kyuucr/Neptunewire/STLS/Gantry/XZ_Axis/X_Carriage/probe_retainer_bracket.stl

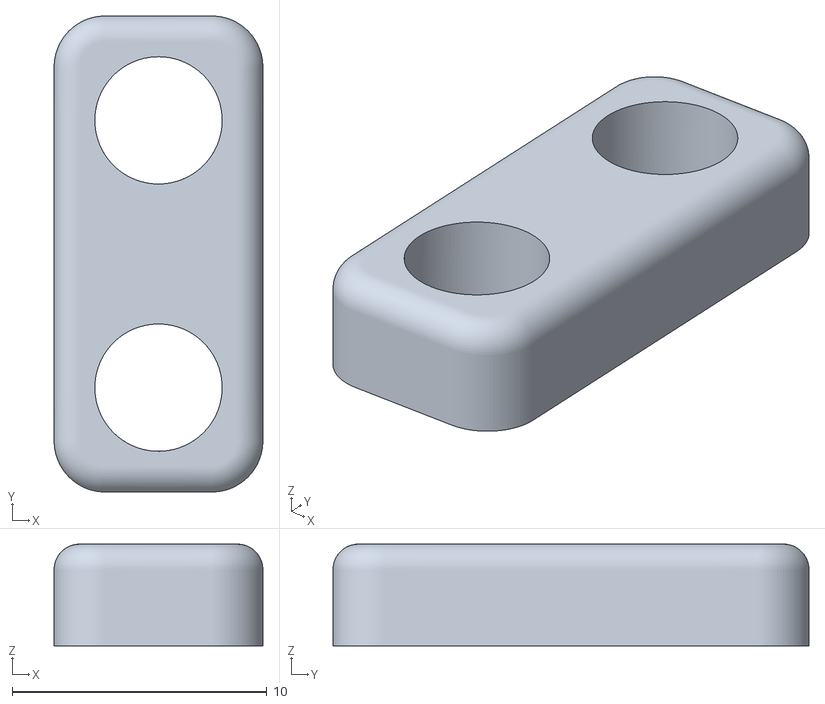
[picture p15: CAD file, 2026-07-10]
STLS/Gantry/XZ_Axis/X_Carriage/probe_retainer_bracket.stl
8.20 x 18.7 x 4.00
