kyuucr/Neptunewire/STLS/Gantry/Y_Axis/[a]_y_chain_frame_mount_igus.stl

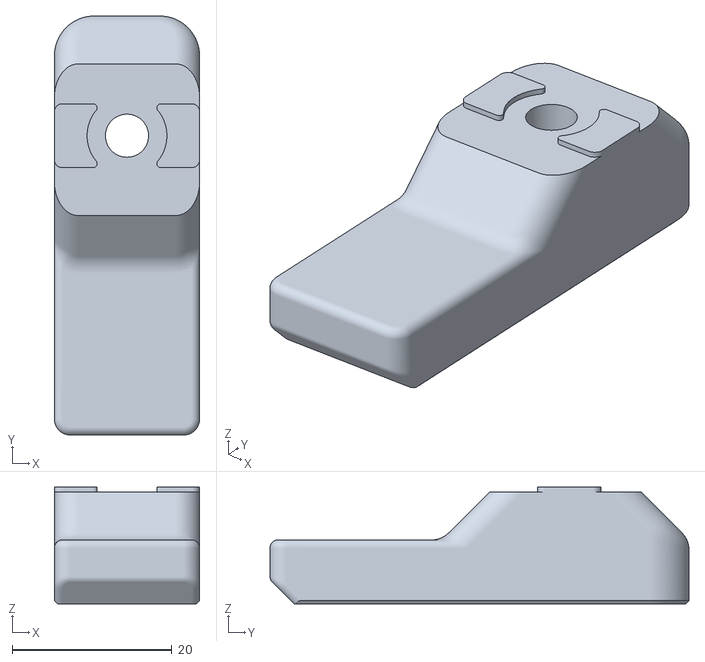
[picture p16: CAD file, 2026-07-10]
STLS/Gantry/Y_Axis/[a]_y_chain_frame_mount_igus.stl
18.2 x 52.5 x 14.6
