kyuucr/Neptunewire/STLS/Grills/grill_rear_left.stl

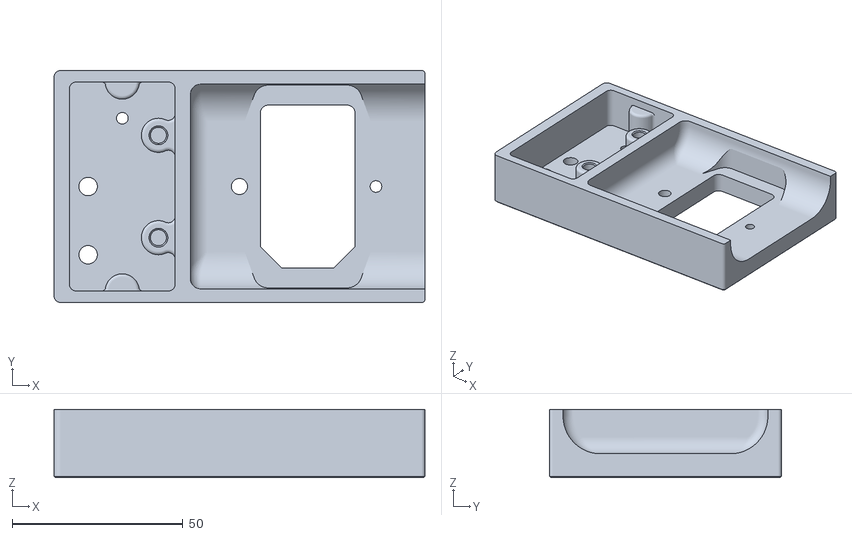
[picture p17: CAD file, 2026-07-10]
STLS/Grills/grill_rear_left.stl
108.7 x 68.0 x 20.0
