kyuucr/Neptunewire/STLS/Panel_Mounting/Doors/top_door_latch.stl

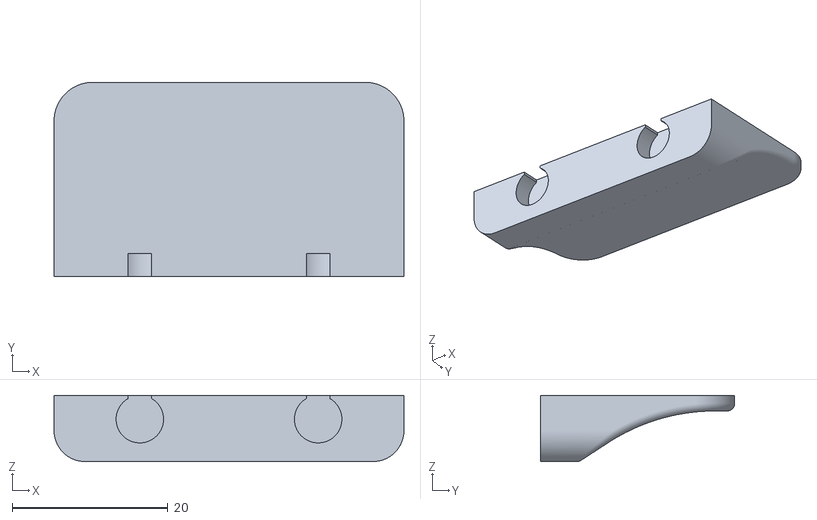
[picture p18: CAD file, 2026-07-10]
STLS/Panel_Mounting/Doors/top_door_latch.stl
45.0 x 25.0 x 8.50
