kyuucr/Neptunewire/STLS/Panel_Mounting/side_strap_x4.stl

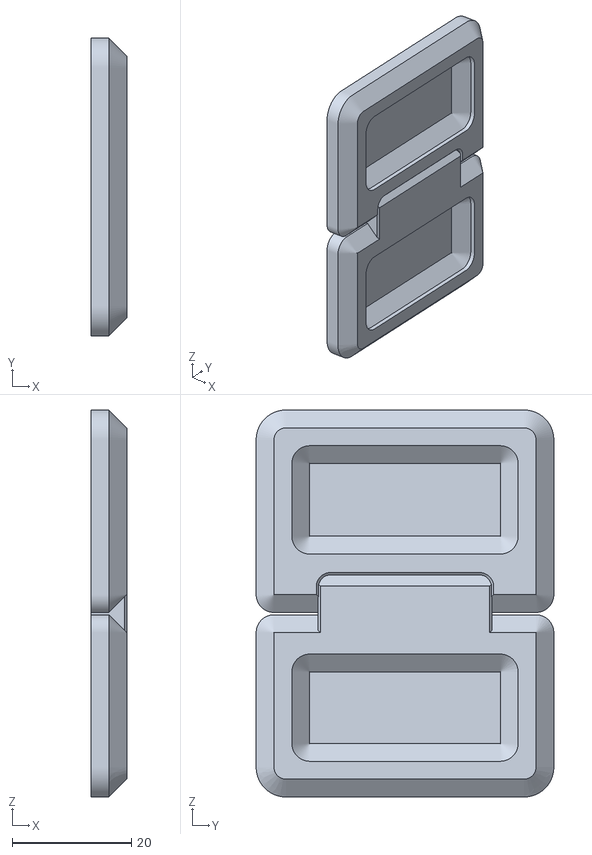
[picture p19: CAD file, 2026-07-10]
STLS/Panel_Mounting/side_strap_x4.stl
6.00 x 50.0 x 65.0
