kyuucr/Neptunewire/STLS/Decks_Printable/deck_right_front.stl

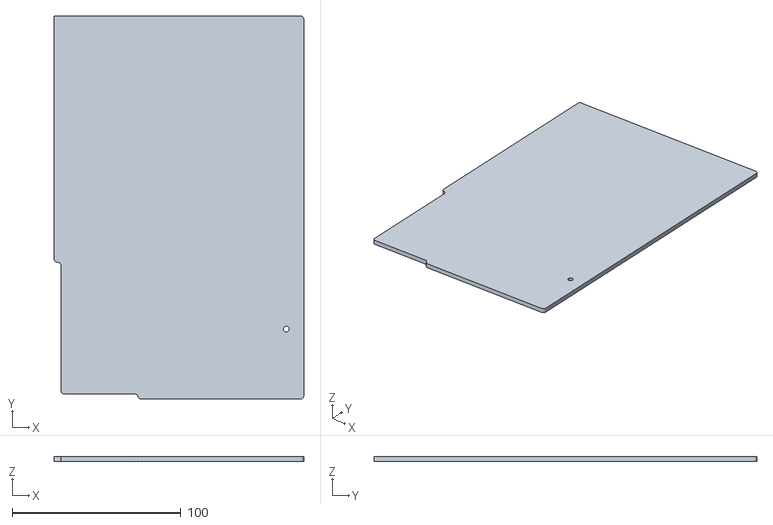
[picture p20: CAD file, 2026-07-10]
STLS/Decks_Printable/deck_right_front.stl
148.0 x 227.0 x 3.00
