kyuucr/Neptunewire/STLS/Electronics/PS_board_4040_mount.stl

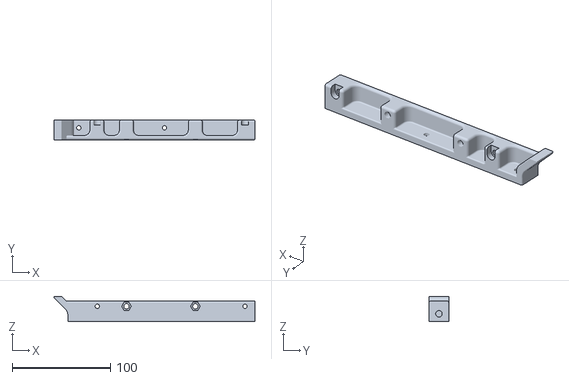
[picture p21: CAD file, 2026-07-10]
STLS/Electronics/PS_board_4040_mount.stl
204.2 x 20.1 x 25.8
