kyuucr/Neptunewire/STLS/Extensions/rear_extension_right_a.stl

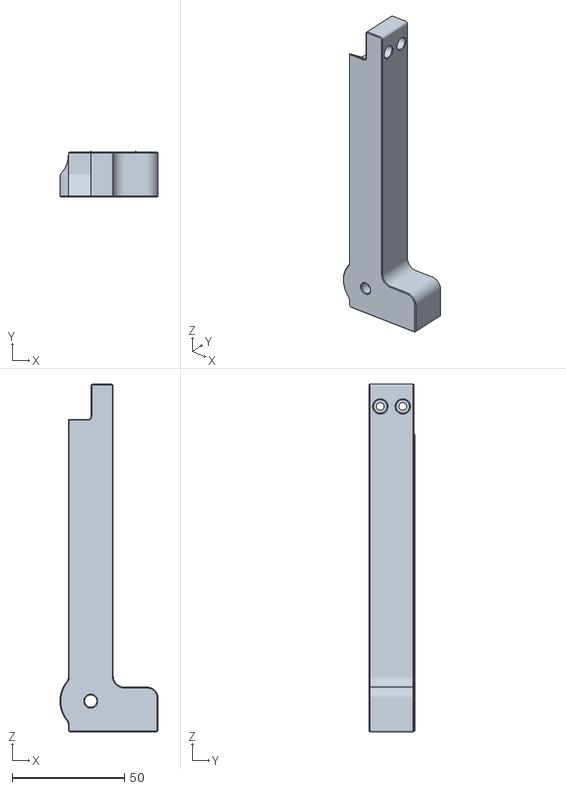
[picture p22: CAD file, 2026-07-10]
STLS/Extensions/rear_extension_right_a.stl
43.8 x 20.4 x 154.9
