kyuucr/Neptunewire/STLS/Gantry/XZ_Axis/X_Carriage/[a]_x_bearing_block.stl

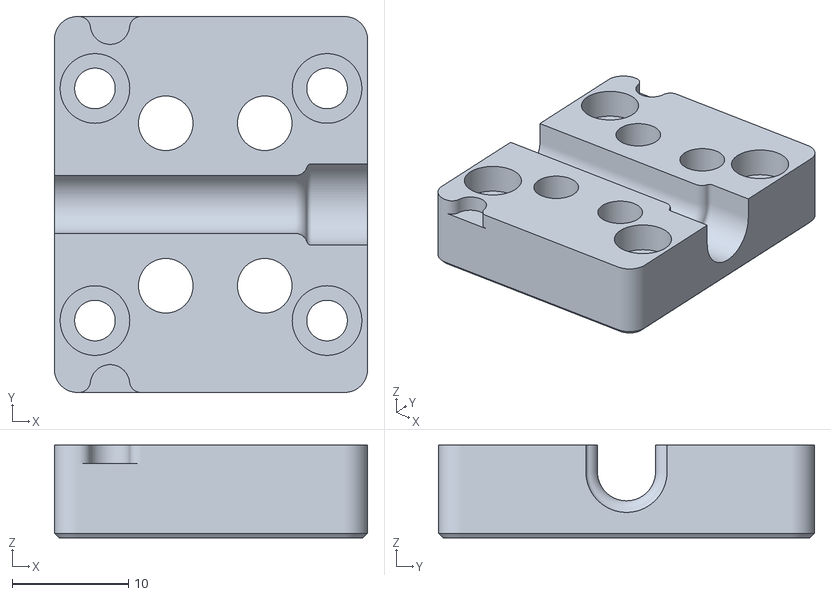
[picture p23: CAD file, 2026-07-10]
STLS/Gantry/XZ_Axis/X_Carriage/[a]_x_bearing_block.stl
27.0 x 32.4 x 8.00
