kyuucr/Neptunewire/STLS/Gantry/XZ_Axis/x_motor_mount_b.stl

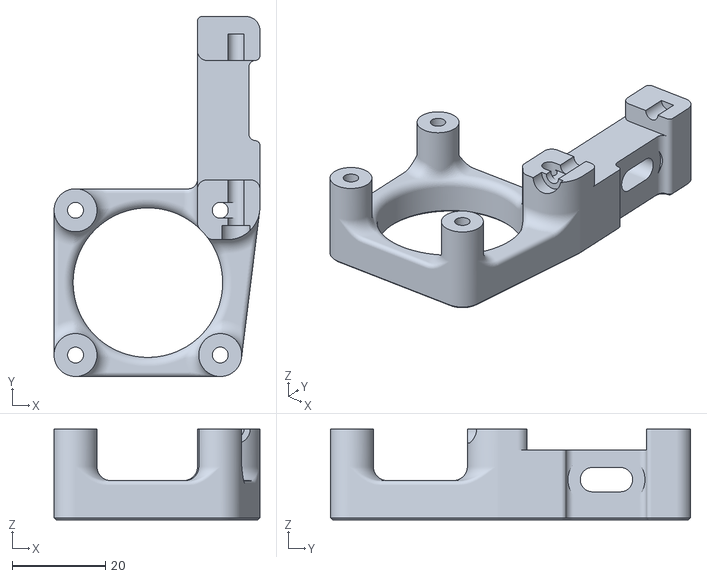
[picture p24: CAD file, 2026-07-10]
STLS/Gantry/XZ_Axis/x_motor_mount_b.stl
44.1 x 77.1 x 19.4
