kyuucr/Neptunewire/STLS/Gantry/Y_Axis/[a]_y_chain_bed_mount_generic.stl

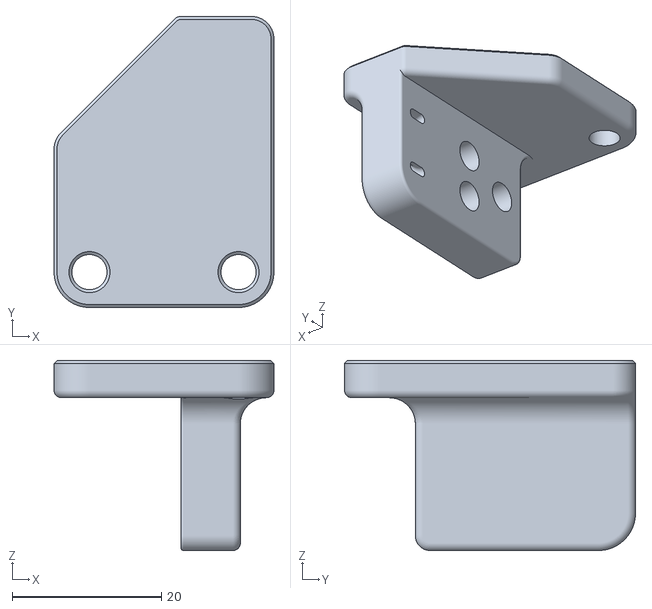
[picture p25: CAD file, 2026-07-10]
STLS/Gantry/Y_Axis/[a]_y_chain_bed_mount_generic.stl
29.5 x 39.0 x 25.5
