kyuucr/Neptunewire/STLS/Grills/grill_front_middle.stl

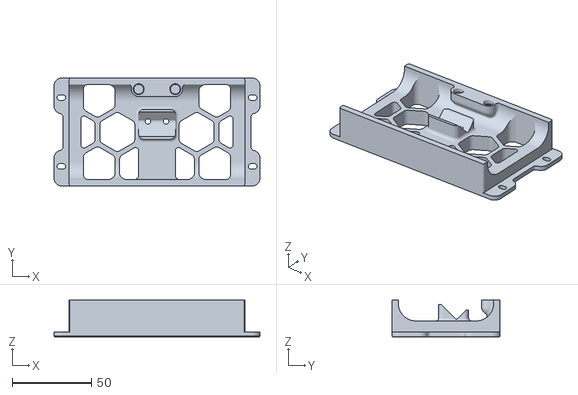
[picture p26: CAD file, 2026-07-10]
STLS/Grills/grill_front_middle.stl
129.8 x 68.0 x 23.0
