kyuucr/Neptunewire/STLS/Panel_Mounting/Doors/door_handle_a_x2.stl

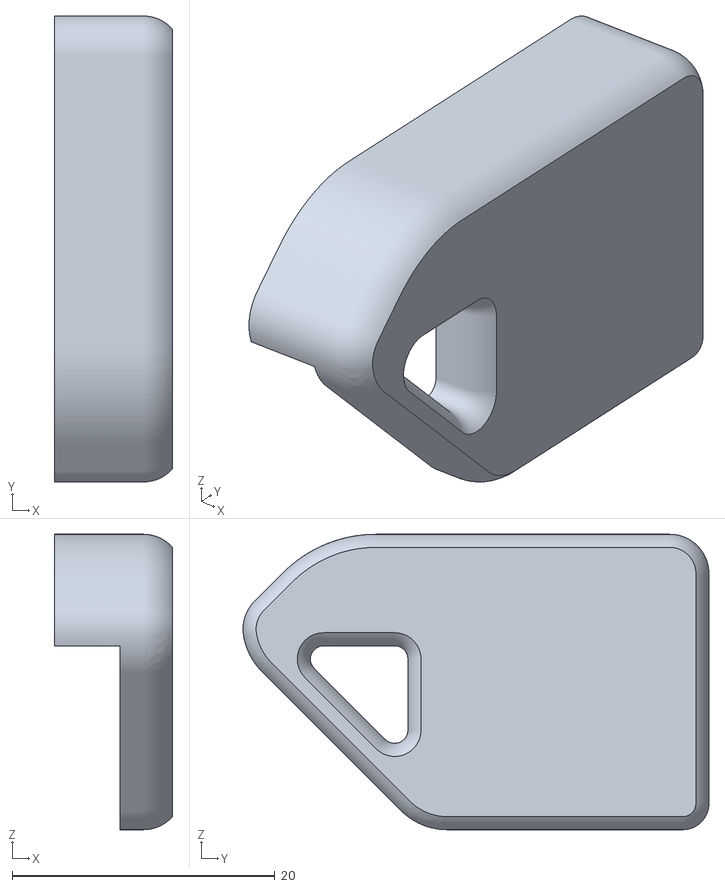
[picture p27: CAD file, 2026-07-10]
STLS/Panel_Mounting/Doors/door_handle_a_x2.stl
9.00 x 35.5 x 22.5
