kyuucr/Neptunewire/STLS/Panel_Mounting/panel_clip_x4.stl

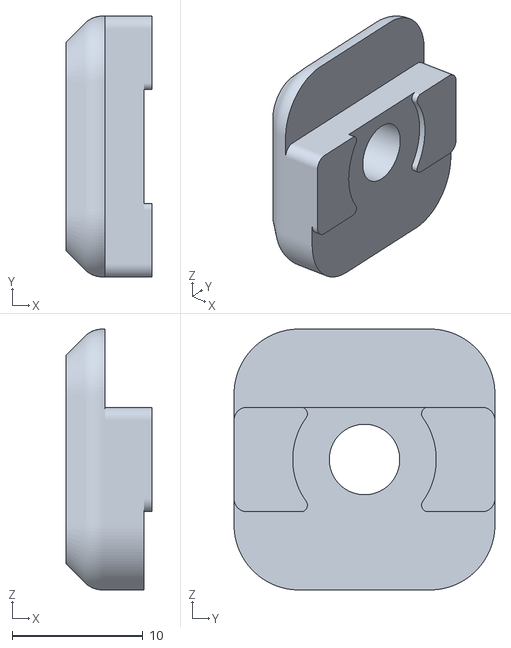
[picture p28: CAD file, 2026-07-10]
STLS/Panel_Mounting/panel_clip_x4.stl
6.60 x 20.0 x 20.0
