kyuucr/Neptunewire/STLS/Electronics/hex_board_frame_skr_pico+fly_utor.stl

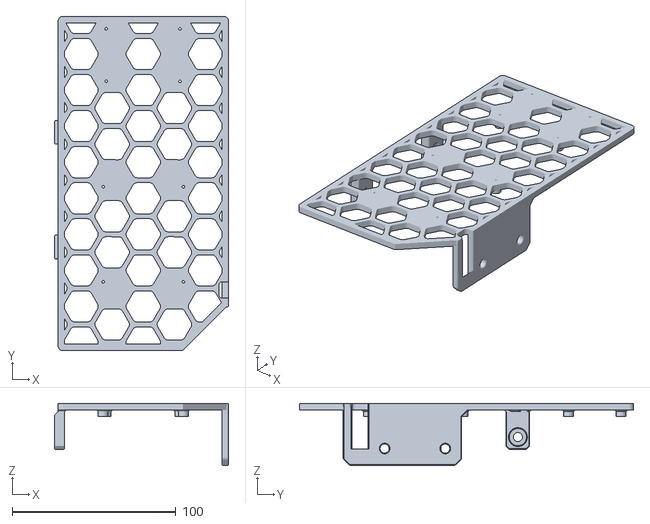
[picture p29: CAD file, 2026-07-10]
STLS/Electronics/hex_board_frame_skr_pico+fly_utor.stl
106.2 x 204.0 x 37.9
