kyuucr/Neptunewire/STLS/Gantry/XZ_Axis/X_Carriage/[a]_xz_belt_clip_x2.stl

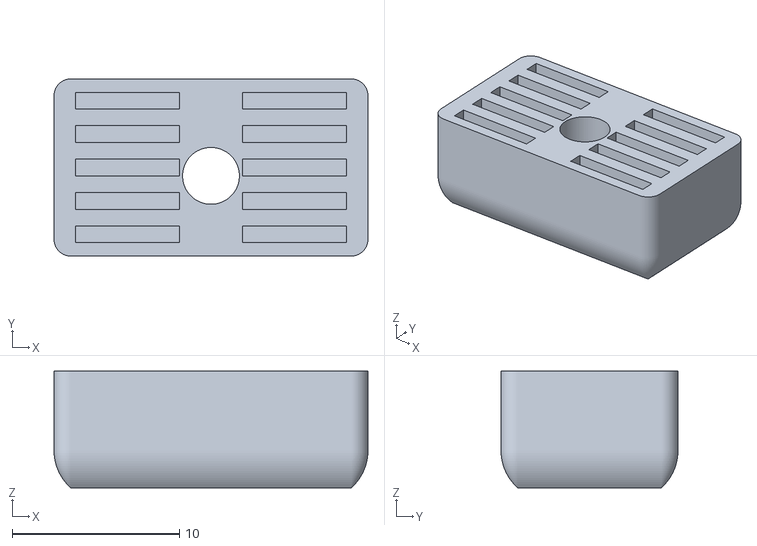
[picture p30: CAD file, 2026-07-10]
STLS/Gantry/XZ_Axis/X_Carriage/[a]_xz_belt_clip_x2.stl
18.8 x 10.6 x 7.00
