kyuucr/Neptunewire/STLS/Gantry/Y_Axis/[a]_y_axis_ls_mount.stl

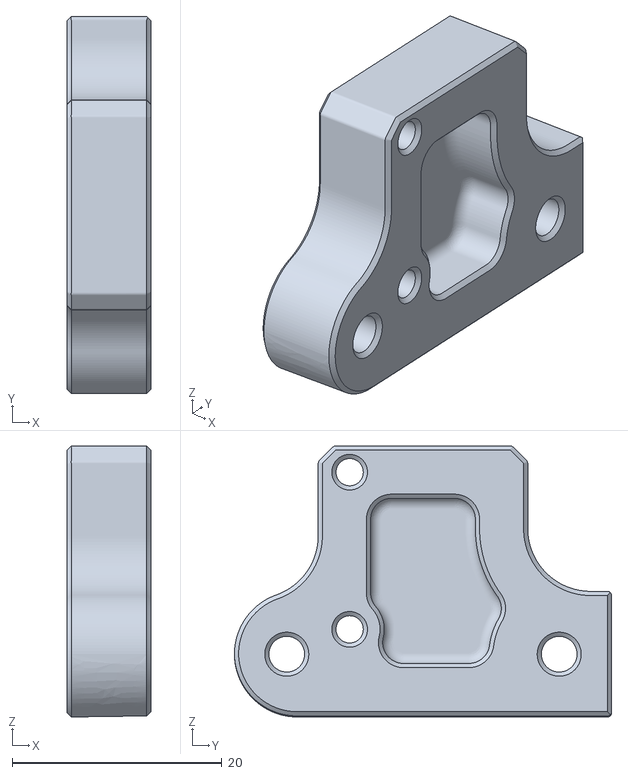
[picture p31: CAD file, 2026-07-10]
STLS/Gantry/Y_Axis/[a]_y_axis_ls_mount.stl
8.00 x 36.0 x 25.9
