kyuucr/Neptunewire/STLS/Grills/grill_rear_middle.stl

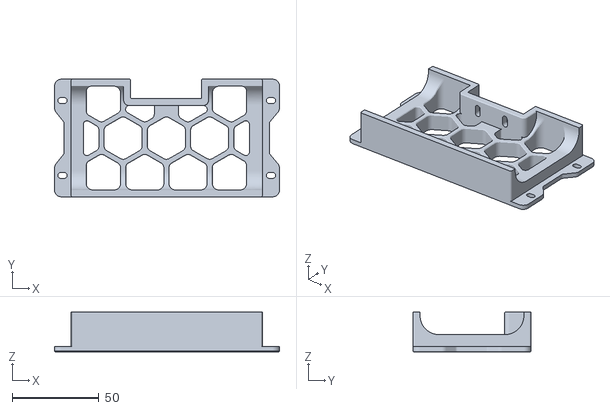
[picture p32: CAD file, 2026-07-10]
STLS/Grills/grill_rear_middle.stl
130.0 x 68.0 x 23.0
