kyuucr/Neptunewire/STLS/Panel_Mounting/front_panel_bracket_left.stl

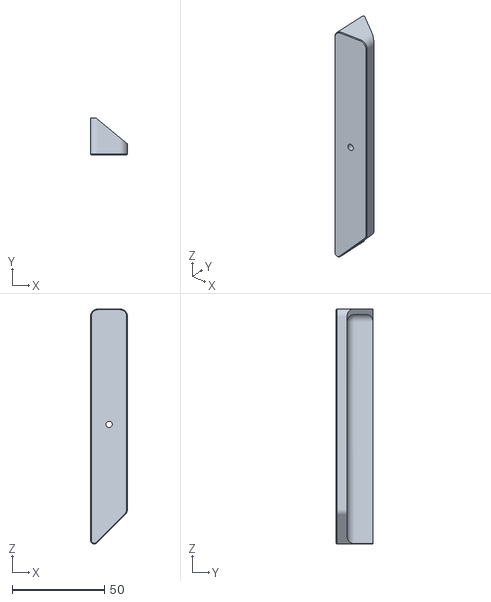
[picture p33: CAD file, 2026-07-10]
STLS/Panel_Mounting/front_panel_bracket_left.stl
20.0 x 20.0 x 127.2
