kyuucr/Neptunewire/STLS/Electronics/hex_board_frame.stl

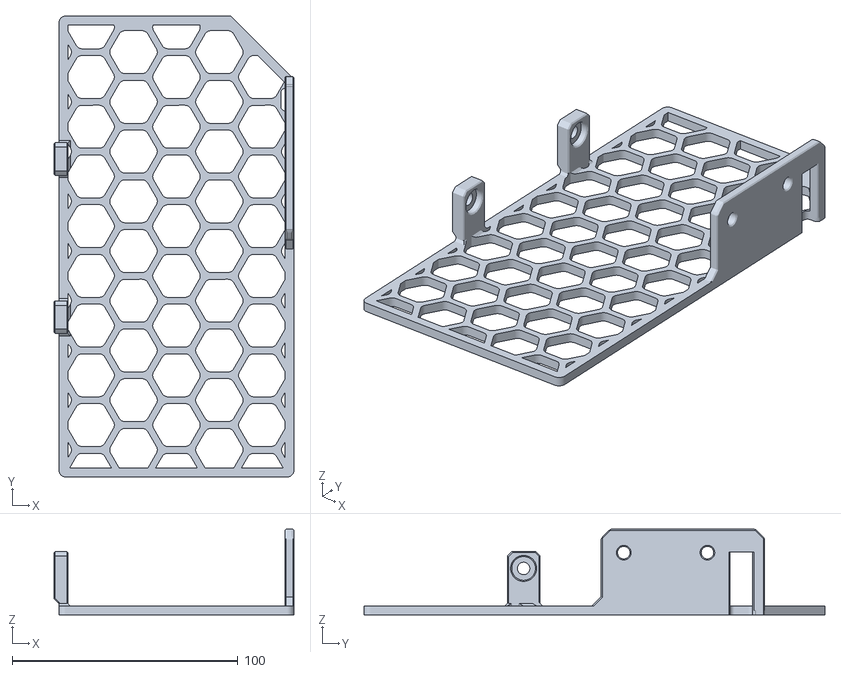
[picture p34: CAD file, 2026-07-10]
STLS/Electronics/hex_board_frame.stl
106.2 x 204.0 x 37.9
