kyuucr/Neptunewire/STLS/Extensions/front_extension_left_b.stl

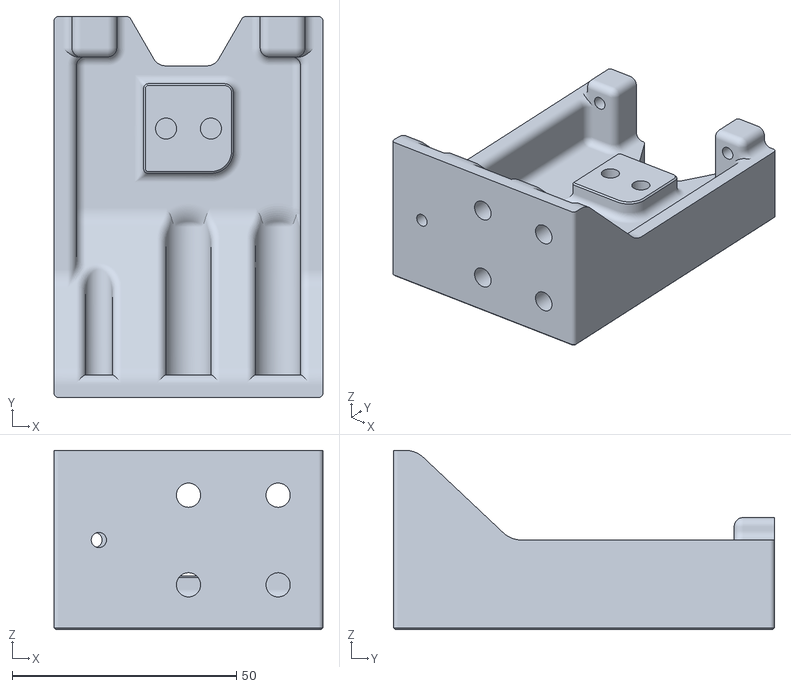
[picture p35: CAD file, 2026-07-10]
STLS/Extensions/front_extension_left_b.stl
60.0 x 85.0 x 40.0
