kyuucr/Neptunewire/STLS/Gantry/XZ_Axis/xz_block_right_b.stl

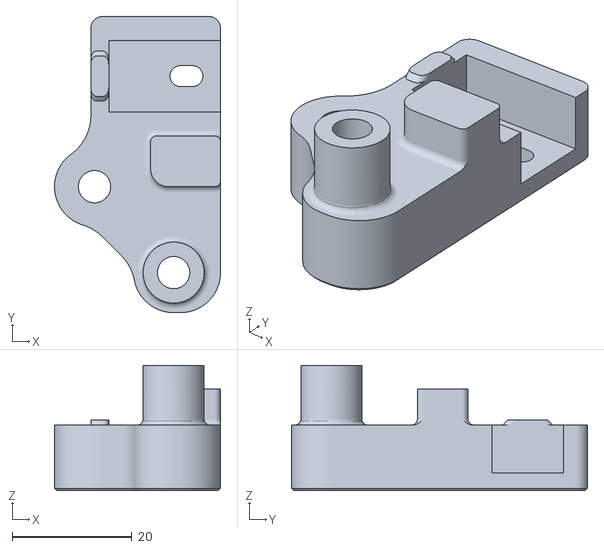
[picture p36: CAD file, 2026-07-10]
STLS/Gantry/XZ_Axis/xz_block_right_b.stl
27.8 x 49.6 x 21.0
