kyuucr/Neptunewire/STLS/Grills/grill_rear_left_shock_blocker.stl

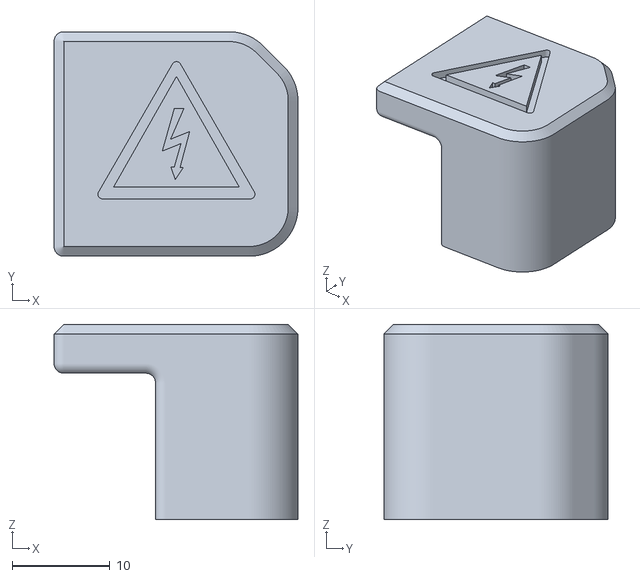
[picture p37: CAD file, 2026-07-10]
STLS/Grills/grill_rear_left_shock_blocker.stl
25.0 x 23.0 x 20.0
