kyuucr/Neptunewire/STLS/Decks_Printable/deck_right_rear.stl

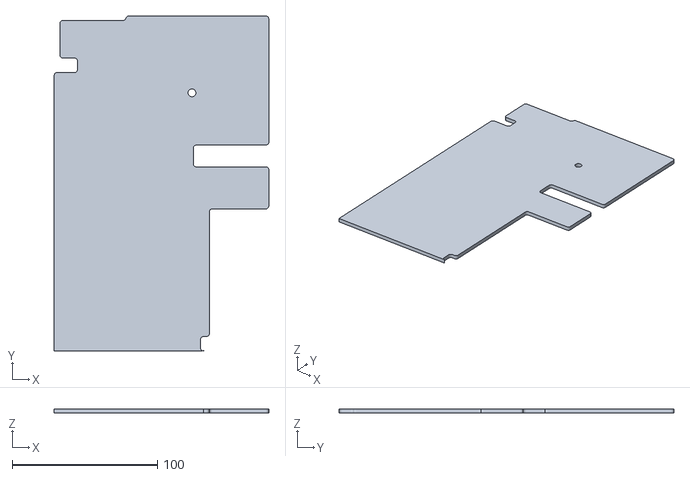
[picture p38: CAD file, 2026-07-10]
STLS/Decks_Printable/deck_right_rear.stl
148.0 x 231.0 x 3.00
