kyuucr/Neptunewire/STLS/Extensions/rear_extension_left_b.stl

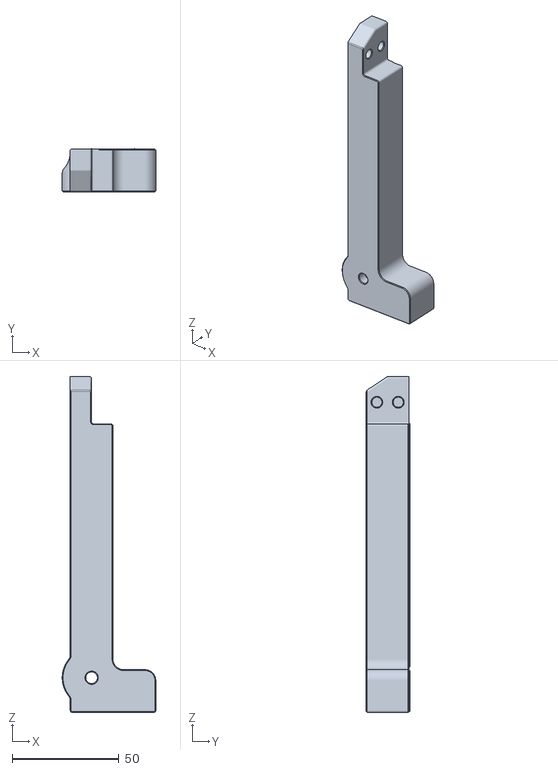
[picture p39: CAD file, 2026-07-10]
STLS/Extensions/rear_extension_left_b.stl
43.7 x 20.4 x 157.1
