kyuucr/Neptunewire/STLS/Gantry/XZ_Axis/keybak_mount_plate_b.stl

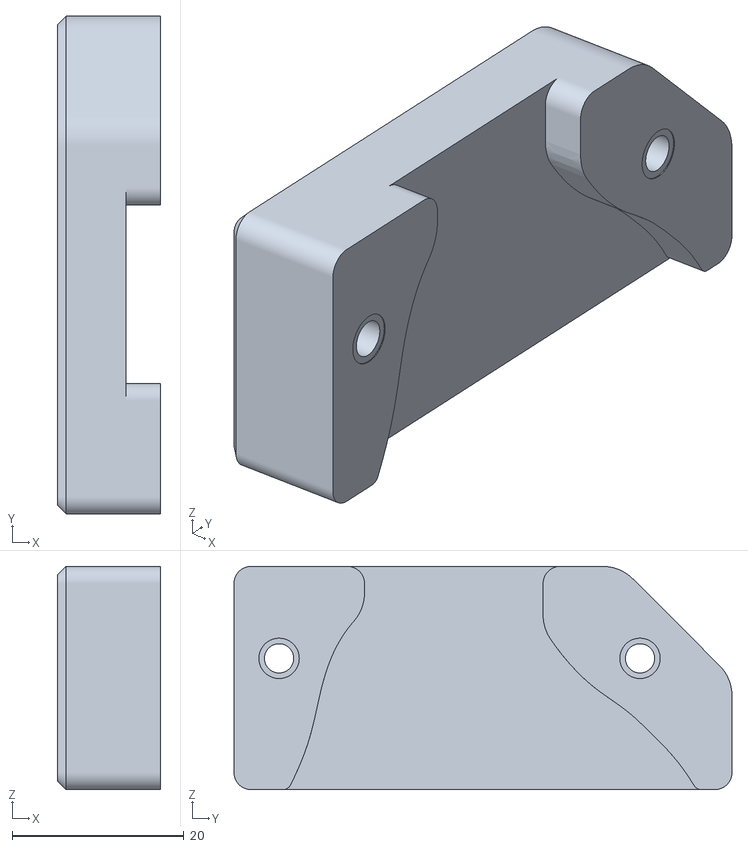
[picture p40: CAD file, 2026-07-10]
STLS/Gantry/XZ_Axis/keybak_mount_plate_b.stl
12.0 x 58.0 x 26.0
