kyuucr/Neptunewire/STLS/Gantry/Y_Axis/y_idler_inner.stl

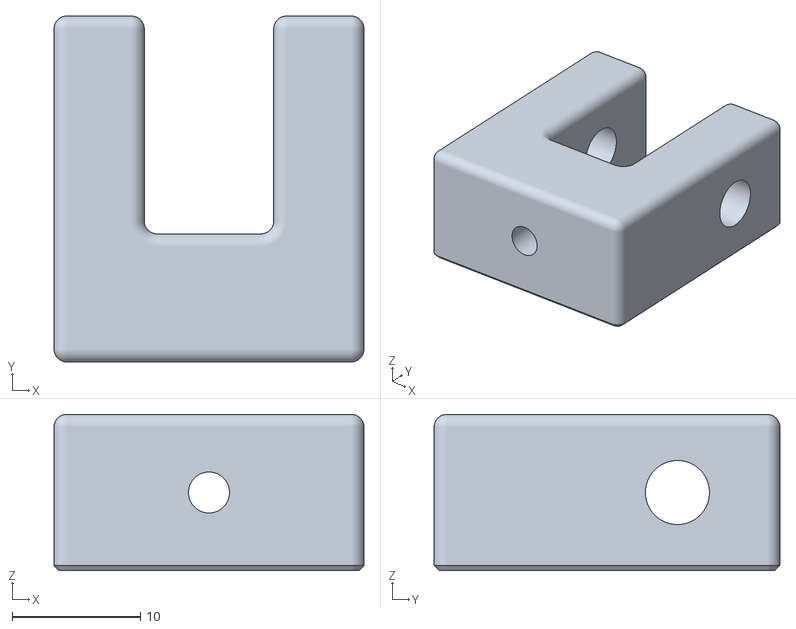
[picture p41: CAD file, 2026-07-10]
STLS/Gantry/Y_Axis/y_idler_inner.stl
24.2 x 27.0 x 12.2
