kyuucr/Neptunewire/STLS/Panel_Mounting/feed_slot.stl

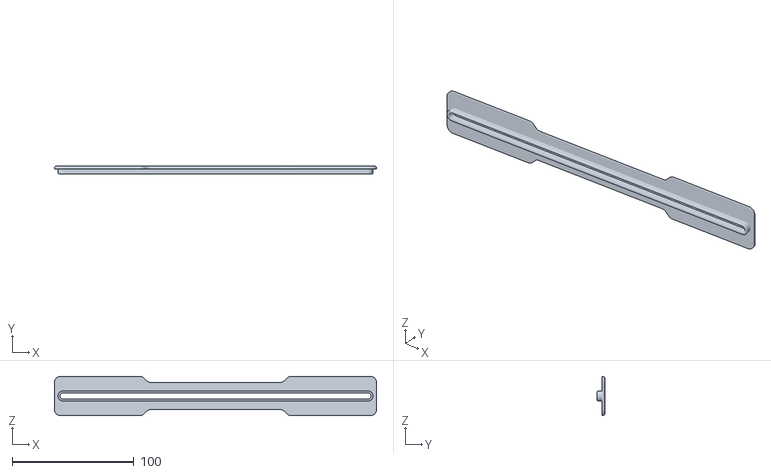
[picture p42: CAD file, 2026-07-10]
STLS/Panel_Mounting/feed_slot.stl
264.0 x 6.40 x 32.2
