kyuucr/Neptunewire/STLS/Gantry/XZ_Axis/keybak_mount_plate_a.stl

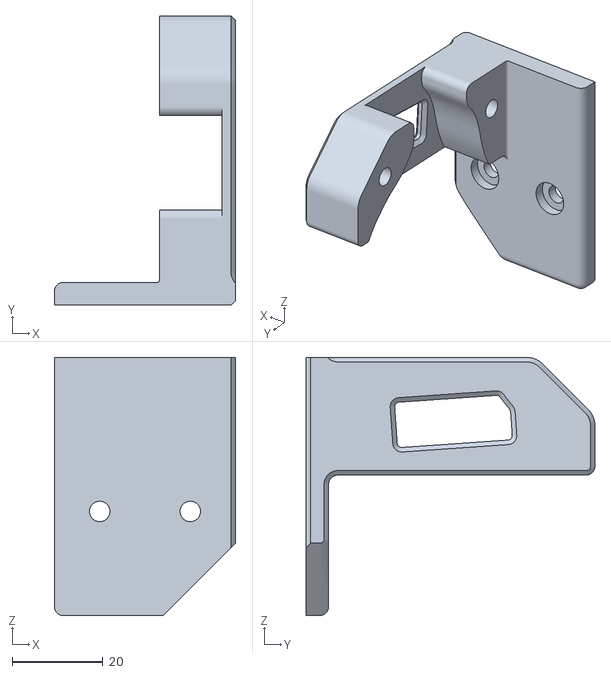
[picture p43: CAD file, 2026-07-10]
STLS/Gantry/XZ_Axis/keybak_mount_plate_a.stl
40.0 x 63.8 x 57.0
