kyuucr/Neptunewire/STLS/Gantry/Y_Axis/y_motor_mount_bracket.stl

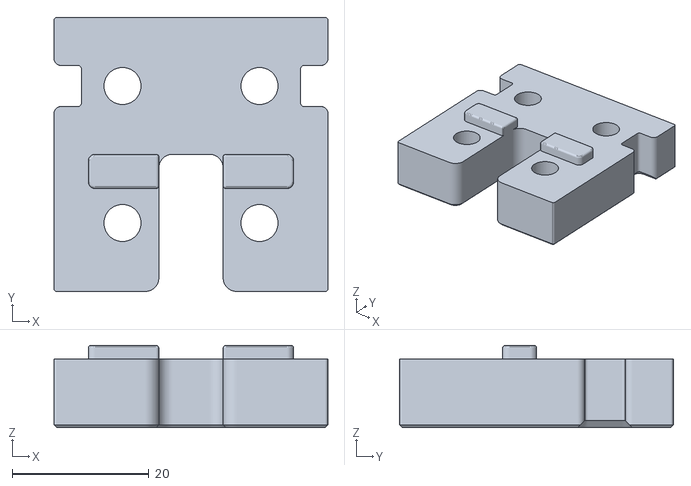
[picture p44: CAD file, 2026-07-10]
STLS/Gantry/Y_Axis/y_motor_mount_bracket.stl
40.0 x 40.0 x 12.0
