kyuucr/Neptunewire/STLS/Panel_Mounting/panel_clip_wide_x2.stl

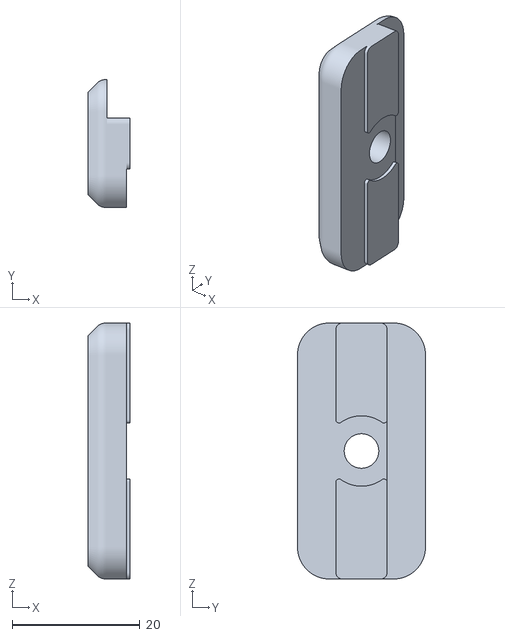
[picture p45: CAD file, 2026-07-10]
STLS/Panel_Mounting/panel_clip_wide_x2.stl
6.60 x 20.0 x 40.0
