kyuucr/Neptunewire/STLS/Extensions/extension_hole_plug_x4.stl

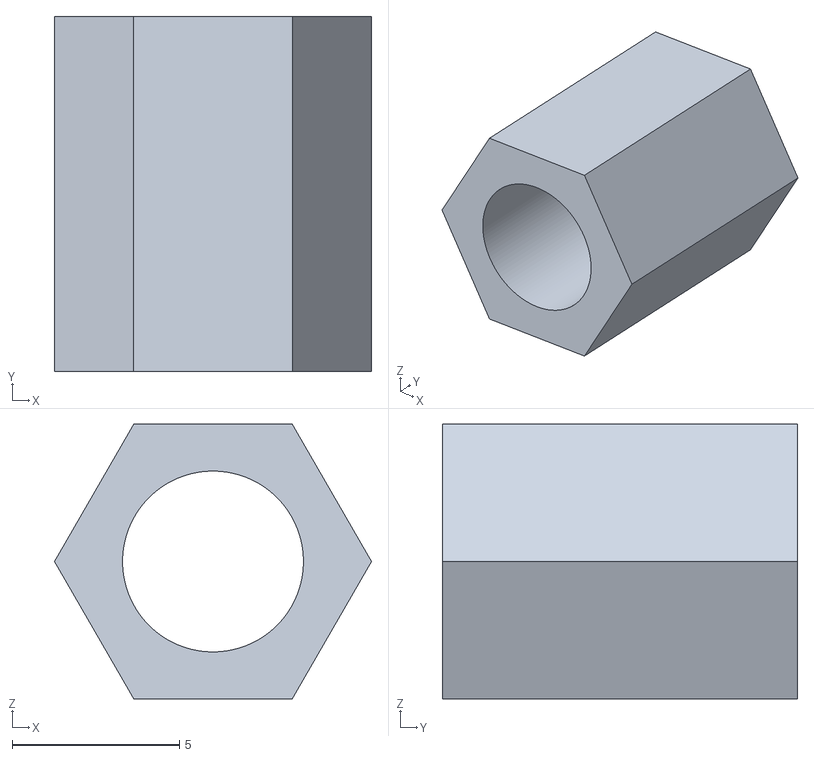
[picture p46: CAD file, 2026-07-10]
STLS/Extensions/extension_hole_plug_x4.stl
9.47 x 10.6 x 8.20
