kyuucr/Neptunewire/STLS/Gantry/XZ_Axis/[a]_z_carriage_stop_bottom_x2.stl

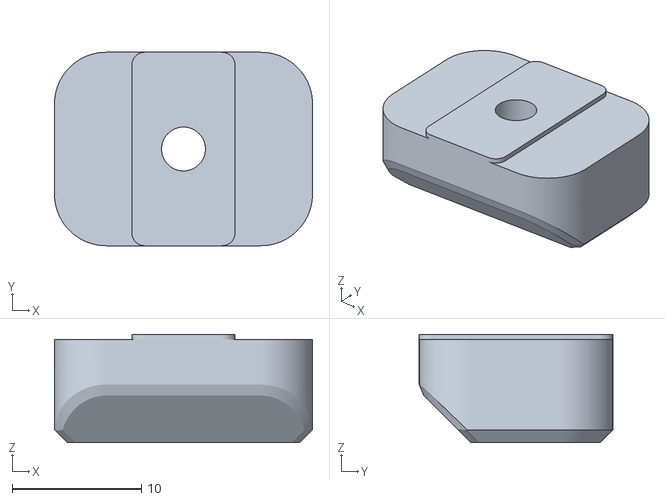
[picture p47: CAD file, 2026-07-10]
STLS/Gantry/XZ_Axis/[a]_z_carriage_stop_bottom_x2.stl
20.0 x 15.0 x 8.40
