kyuucr/Neptunewire/STLS/Gantry/Y_Axis/[a]_y_belt_clip_x2.stl

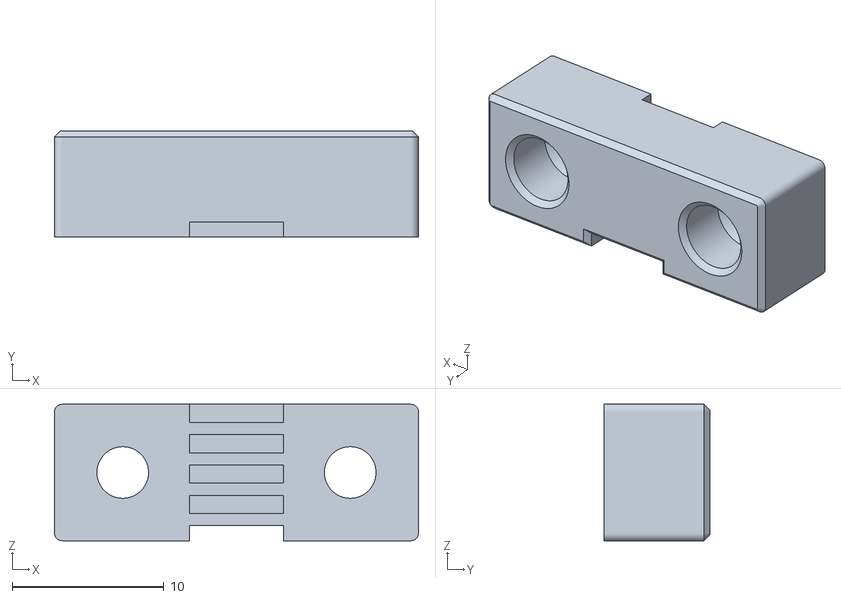
[picture p48: CAD file, 2026-07-10]
STLS/Gantry/Y_Axis/[a]_y_belt_clip_x2.stl
24.0 x 7.00 x 9.00
