kyuucr/Neptunewire/STLS/Grills/grill_rear_right.stl

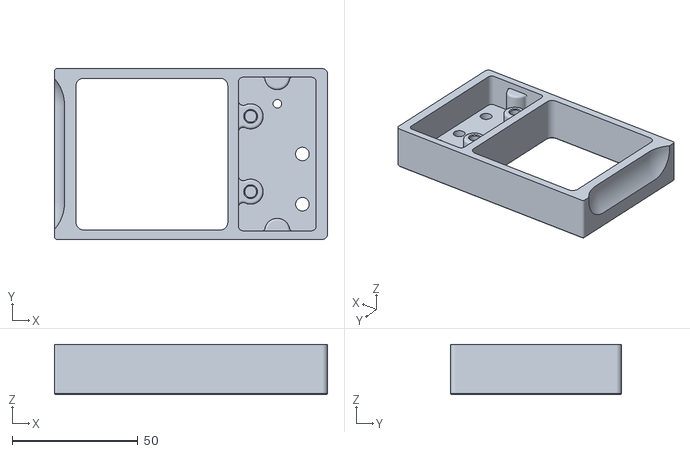
[picture p49: CAD file, 2026-07-10]
STLS/Grills/grill_rear_right.stl
108.7 x 68.0 x 20.0
