kyuucr/Neptunewire/STLS/Panel_Mounting/light_bar_x2.stl

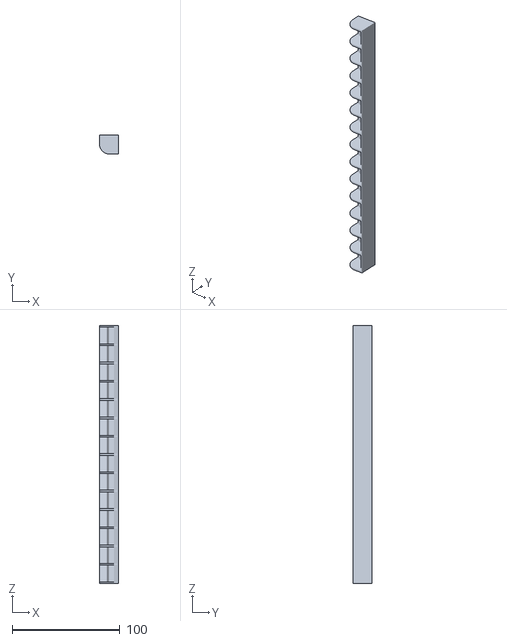
[picture p50: CAD file, 2026-07-10]
STLS/Panel_Mounting/light_bar_x2.stl
18.0 x 18.0 x 239.6
