kyuucr/Neptunewire/STLS/Gantry/XZ_Axis/[a]_upper_idler_support_b_left.stl

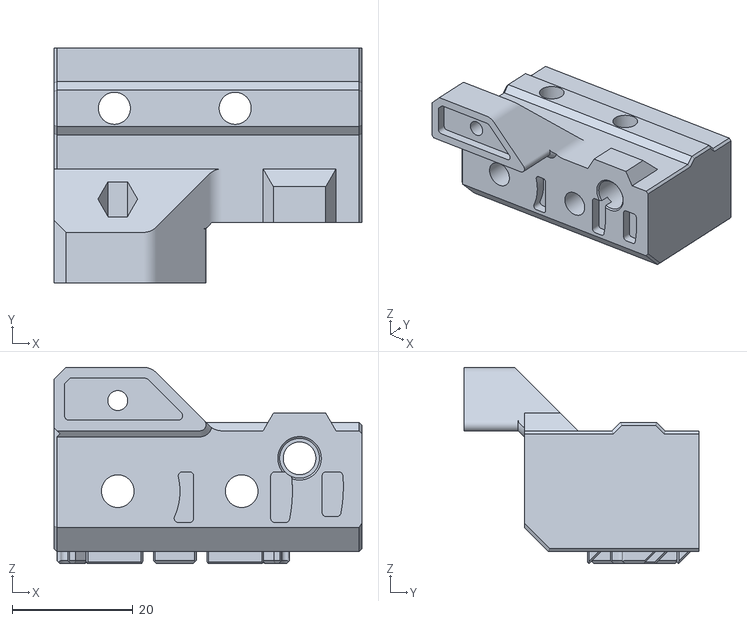
[picture p51: CAD file, 2026-07-10]
STLS/Gantry/XZ_Axis/[a]_upper_idler_support_b_left.stl
51.0 x 38.9 x 32.5
