kyuucr/Neptunewire/STLS/Gantry/Y_Axis/y_axis_bed_carriage_a.stl

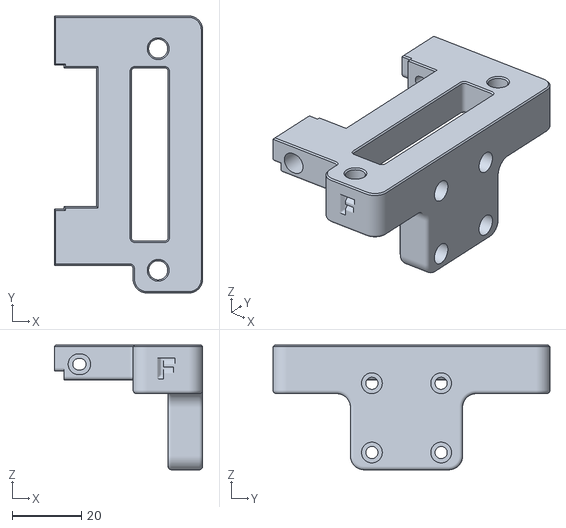
[picture p52: CAD file, 2026-07-10]
STLS/Gantry/Y_Axis/y_axis_bed_carriage_a.stl
42.8 x 80.0 x 36.0
