kyuucr/Neptunewire/STLS/Grills/[a]_grill_endcap_x4.stl

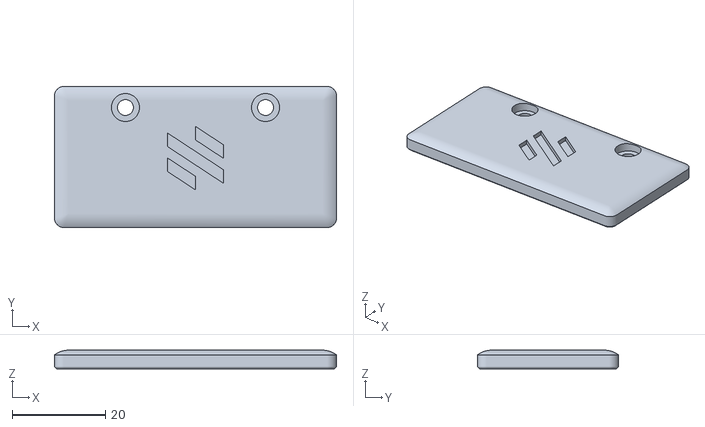
[picture p53: CAD file, 2026-07-10]
STLS/Grills/[a]_grill_endcap_x4.stl
60.4 x 30.2 x 4.00
