kyuucr/Neptunewire/STLS/Gantry/XZ_Axis/[a]_zx_cable_cover.stl

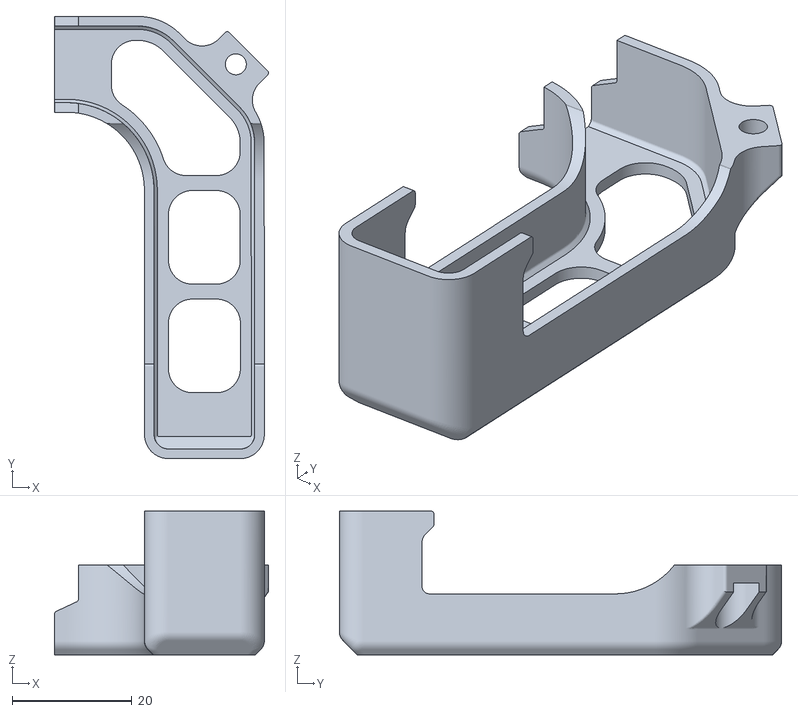
[picture p54: CAD file, 2026-07-10]
STLS/Gantry/XZ_Axis/[a]_zx_cable_cover.stl
35.7 x 73.8 x 24.0
