kyuucr/Neptunewire/STLS/Gantry/XZ_Axis/upper_idler_support_a_left.stl

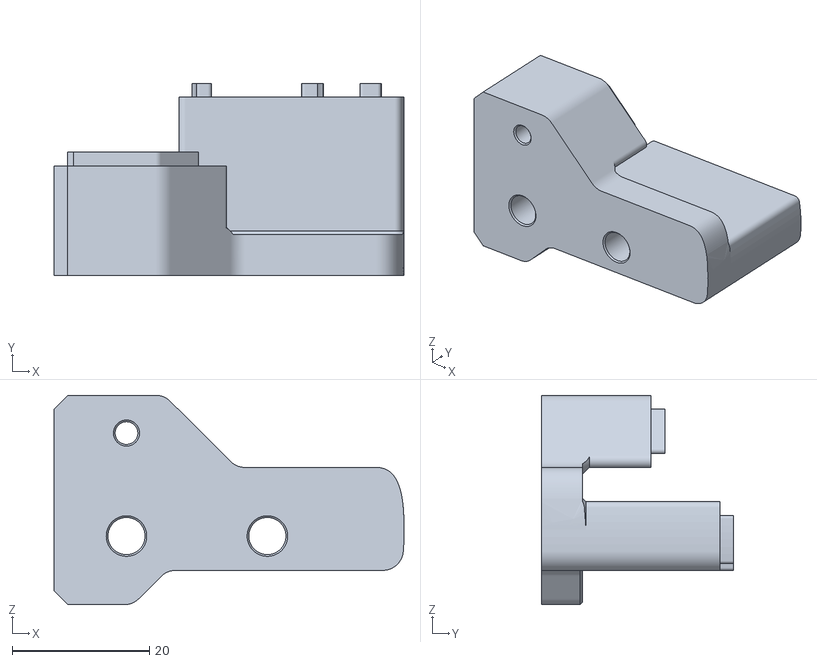
[picture p55: CAD file, 2026-07-10]
STLS/Gantry/XZ_Axis/upper_idler_support_a_left.stl
51.0 x 28.0 x 30.5
