kyuucr/Neptunewire/STLS/Gantry/XZ_Axis/z_bearing_block_right_generic.stl

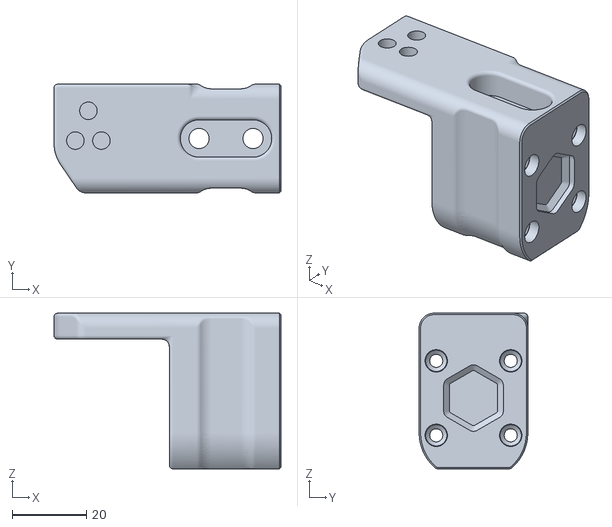
[picture p57: CAD file, 2026-07-10]
STLS/Gantry/XZ_Axis/z_bearing_block_right_generic.stl
60.9 x 29.2 x 41.8
