kyuucr/Neptunewire/STLS/Gantry/Y_Axis/y_idler_b.stl

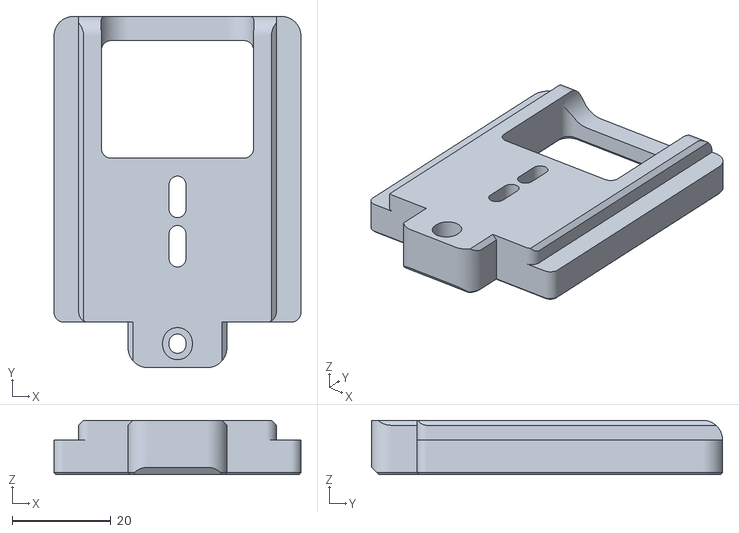
[picture p58: CAD file, 2026-07-10]
STLS/Gantry/Y_Axis/y_idler_b.stl
50.0 x 71.1 x 11.0
