kyuucr/Neptunewire/STLS/Gantry/Y_Axis/y_motor_mount_a.stl

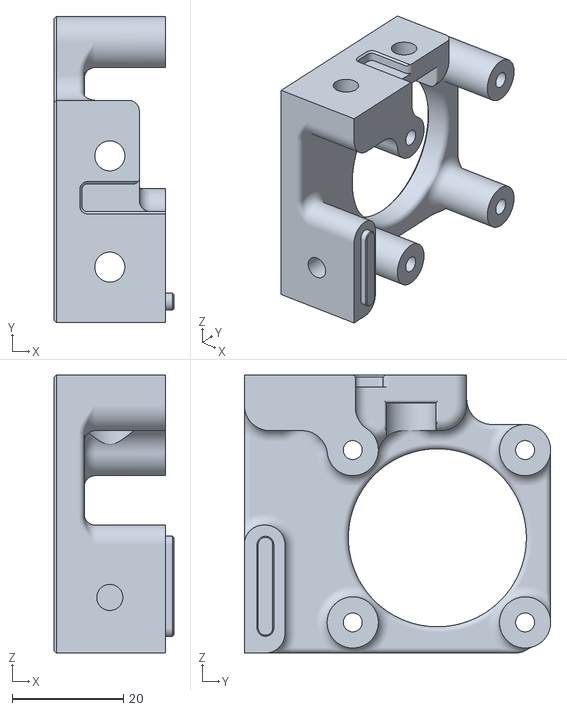
[picture p59: CAD file, 2026-07-10]
STLS/Gantry/Y_Axis/y_motor_mount_a.stl
21.5 x 55.1 x 50.0
