kyuucr/Neptunewire/STLS/Gantry/XZ_Axis/xz_block_left_a.stl

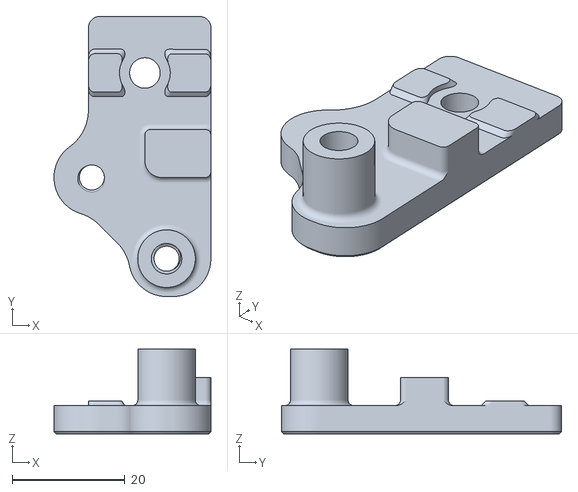
[picture p60: CAD file, 2026-07-10]
STLS/Gantry/XZ_Axis/xz_block_left_a.stl
27.8 x 49.6 x 15.0
