kyuucr/Neptunewire/STLS/Gantry/Y_Axis/y_idler_a.stl

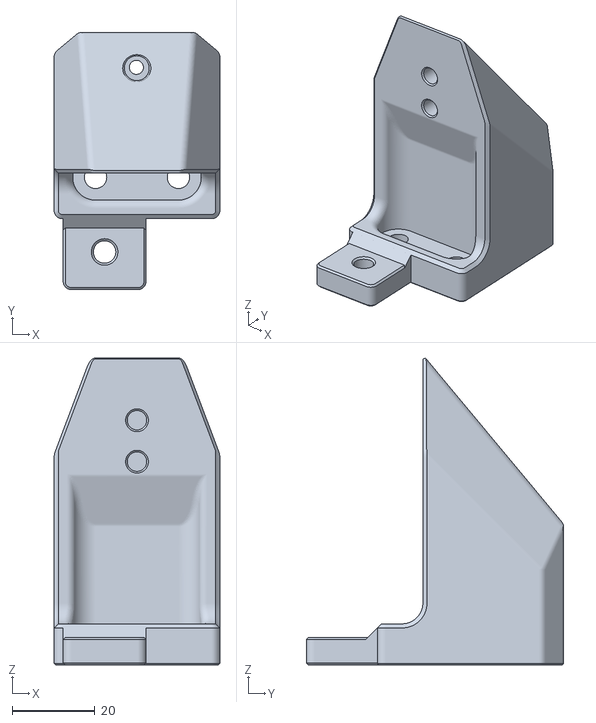
[picture p61: CAD file, 2026-07-10]
STLS/Gantry/Y_Axis/y_idler_a.stl
40.0 x 62.1 x 74.1
