kyuucr/Neptunewire/STLS/Gantry/XZ_Axis/z_bearing_block_right_igus.stl

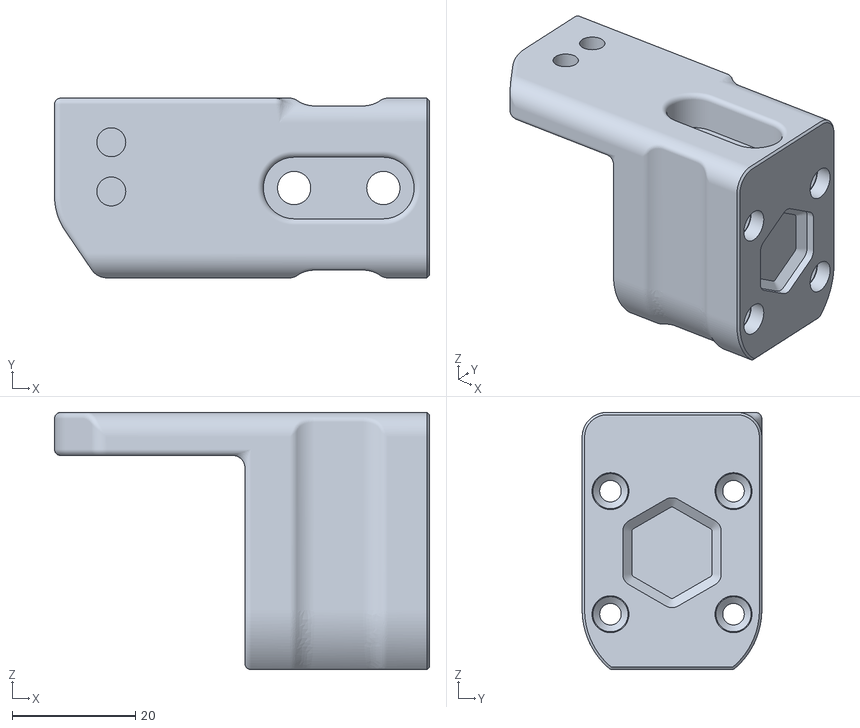
[picture p62: CAD file, 2026-07-10]
STLS/Gantry/XZ_Axis/z_bearing_block_right_igus.stl
60.9 x 29.2 x 41.8
