kyuucr/Neptunewire/STLS/Gantry/Y_Axis/y_axis_bed_carriage_b.stl

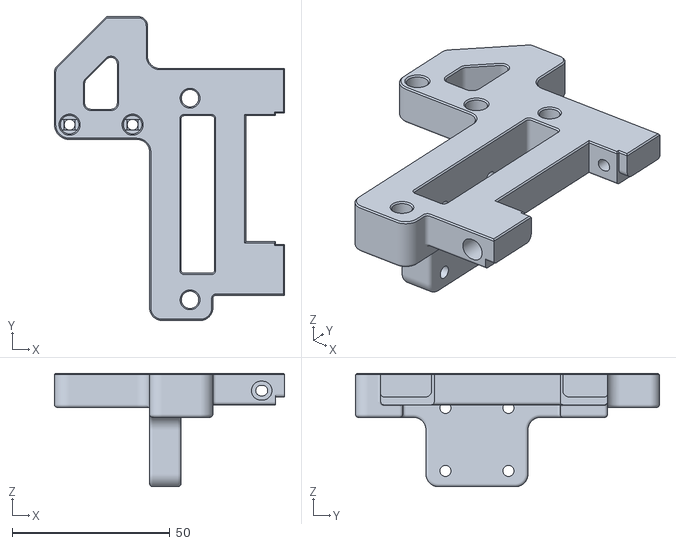
[picture p63: CAD file, 2026-07-10]
STLS/Gantry/Y_Axis/y_axis_bed_carriage_b.stl
73.1 x 96.5 x 36.0
