kyuucr/Neptunewire/STLS/Gantry/XZ_Axis/[a]_xz_tensioner_x2.stl

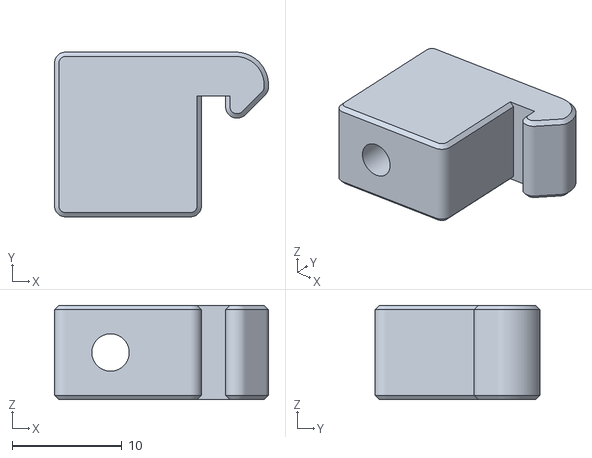
[picture p64: CAD file, 2026-07-10]
STLS/Gantry/XZ_Axis/[a]_xz_tensioner_x2.stl
19.5 x 15.0 x 8.60
