kyuucr/Neptunewire/STLS/Gantry/XZ_Axis/[a]_z_chain_lower_mount_generic.stl

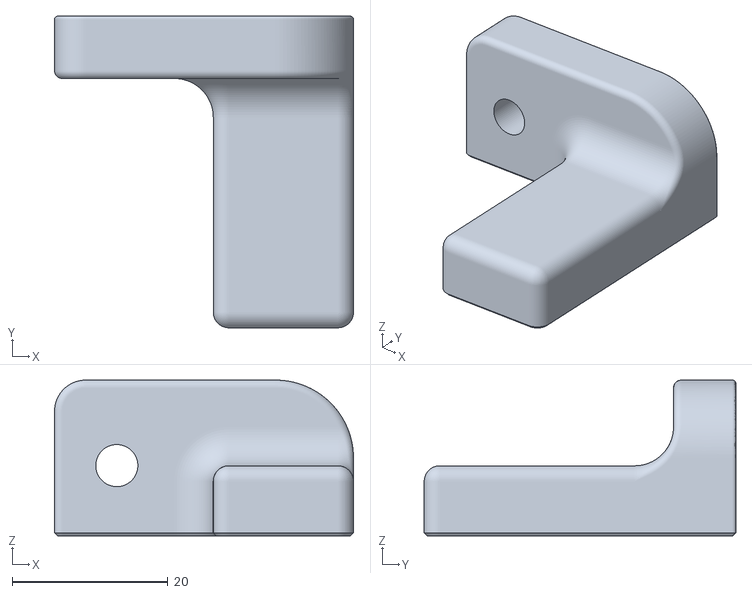
[picture p65: CAD file, 2026-07-10]
STLS/Gantry/XZ_Axis/[a]_z_chain_lower_mount_generic.stl
38.4 x 40.0 x 20.0
