kyuucr/Neptunewire/STLS/Gantry/XZ_Axis/z_bearing_block_left.stl

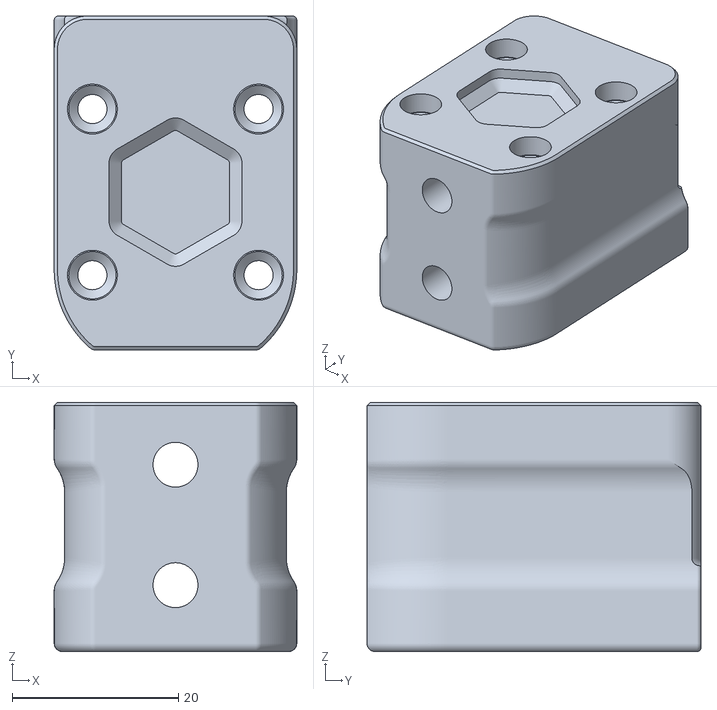
[picture p66: CAD file, 2026-07-10]
STLS/Gantry/XZ_Axis/z_bearing_block_left.stl
29.2 x 40.2 x 30.0
