kyuucr/Neptunewire/STLS/Gantry/XZ_Axis/[a]_upper_idler_support_b_right.stl

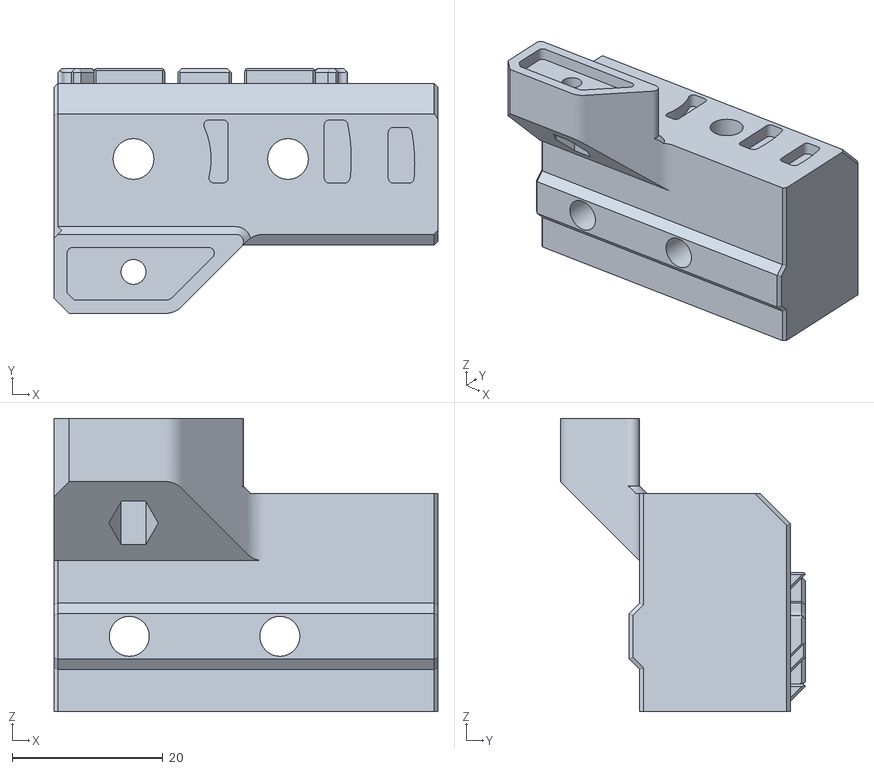
[picture p67: CAD file, 2026-07-10]
STLS/Gantry/XZ_Axis/[a]_upper_idler_support_b_right.stl
51.0 x 32.5 x 38.9
