kyuucr/Neptunewire/STLS/Gantry/XZ_Axis/keybak_idler_bracket.stl

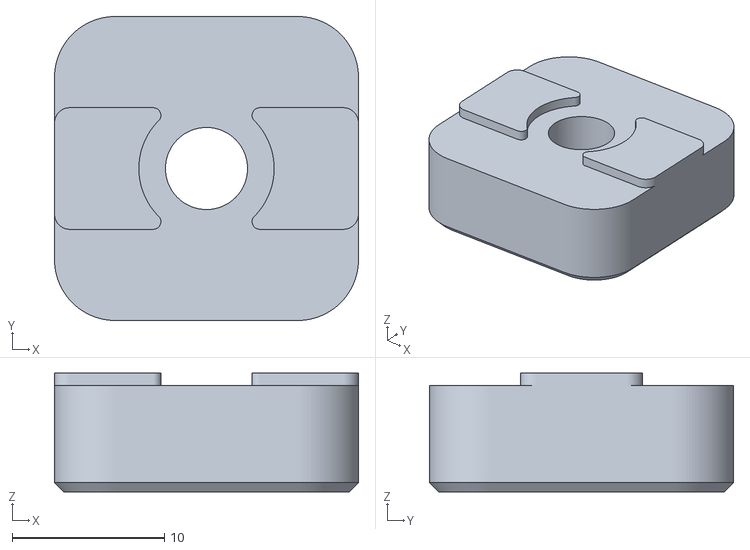
[picture p68: CAD file, 2026-07-10]
STLS/Gantry/XZ_Axis/keybak_idler_bracket.stl
20.0 x 20.0 x 7.80
