kyuucr/Neptunewire/STLS/Gantry/XZ_Axis/[a]_z_chain_lower_mount_igus.stl

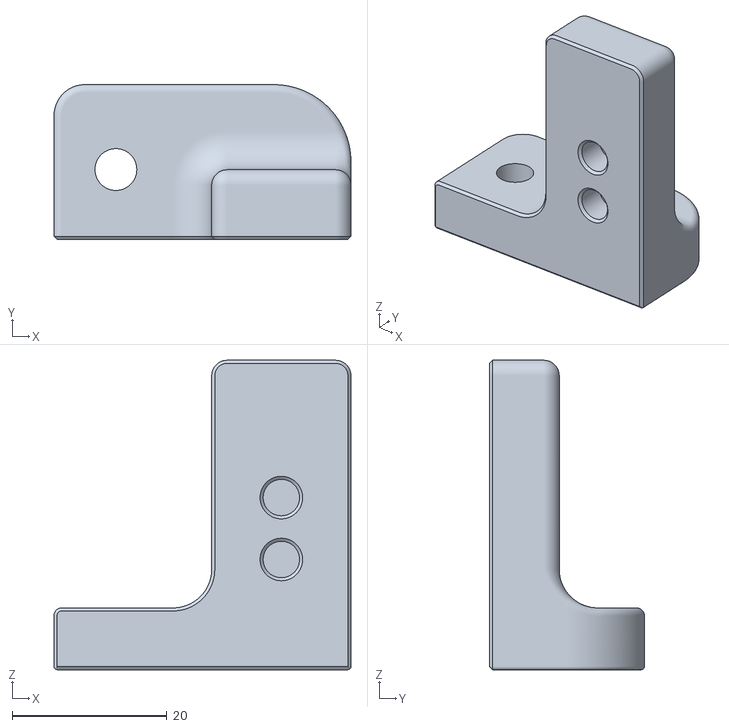
[picture p69: CAD file, 2026-07-10]
STLS/Gantry/XZ_Axis/[a]_z_chain_lower_mount_igus.stl
38.4 x 20.0 x 40.0
